crgarcia12/electronics-homeassistant-lightscontroll/PCB/schematics-v21-esp32s3-pcbway/readme-media/board-pcb2.png

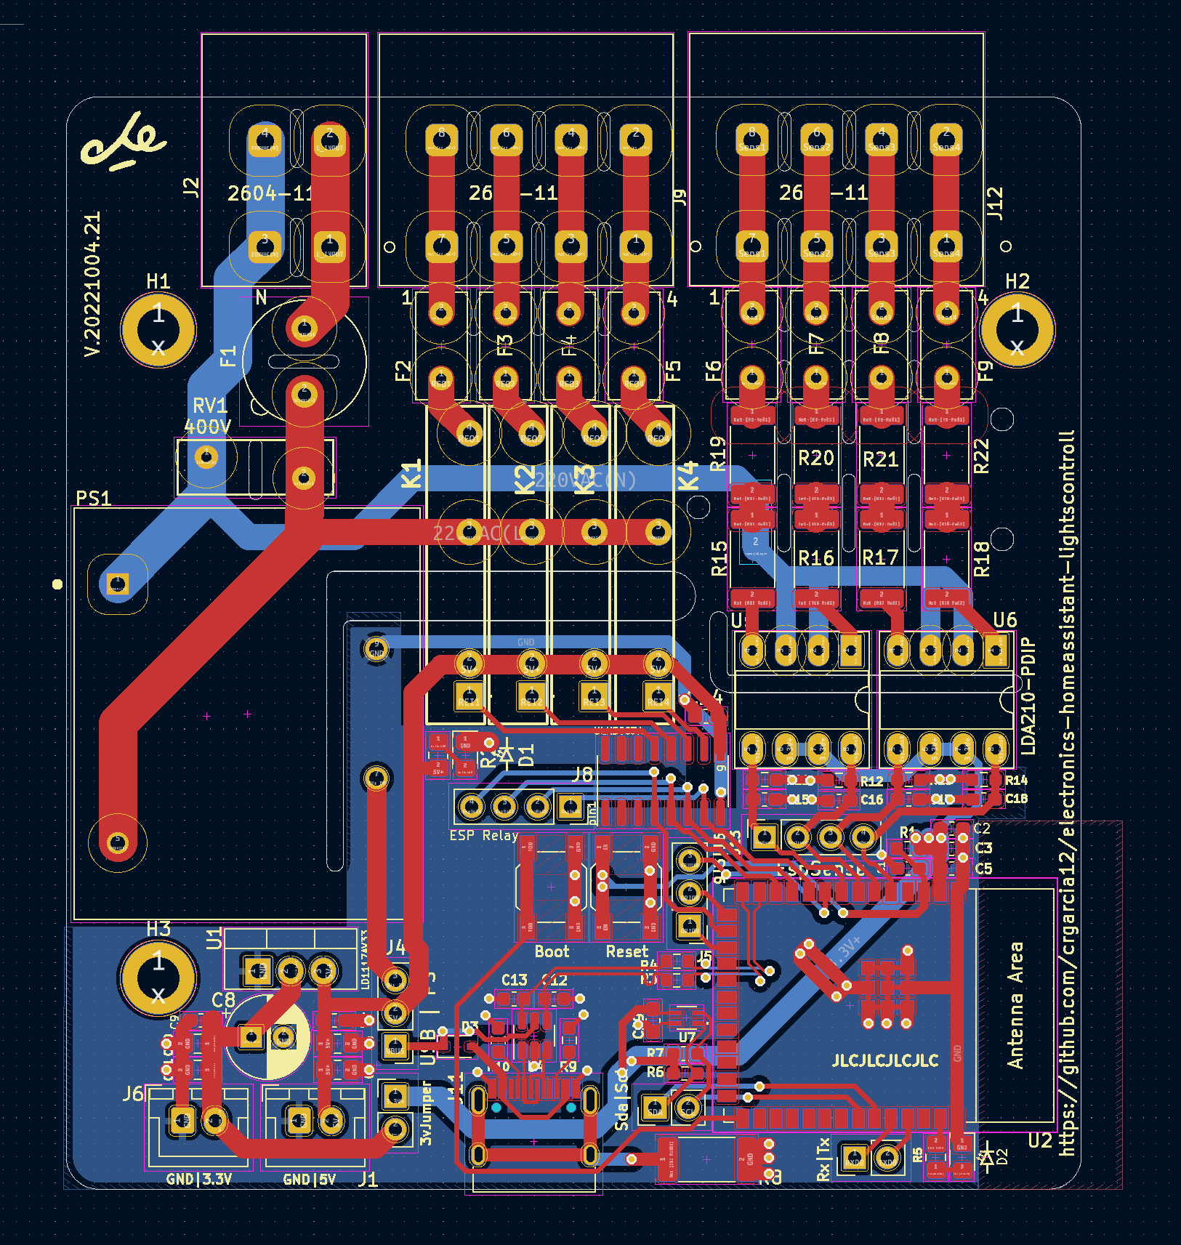
PCB/schematics-v21-esp32s3-pcbway/readme-media/board-pcb2.png
