crgarcia12/electronics-homeassistant-lightscontroll/PCB/schematics-v28.2-jlcpcb/readme-media/board-pcb-3d.jpg

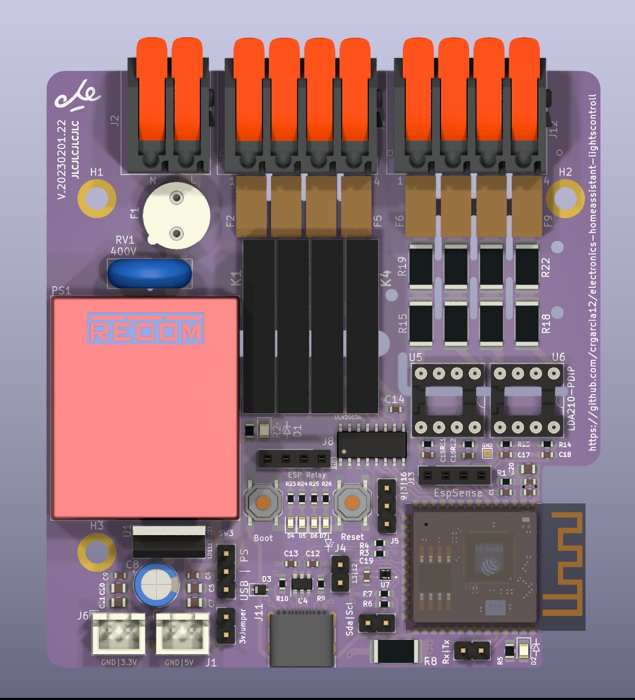
PCB/schematics-v28.2-jlcpcb/readme-media/board-pcb-3d.jpg
