crgarcia12/electronics-homeassistant-lightscontroll/readme-media/main-sensing-analysis/ILD755-22uF-off.jpeg

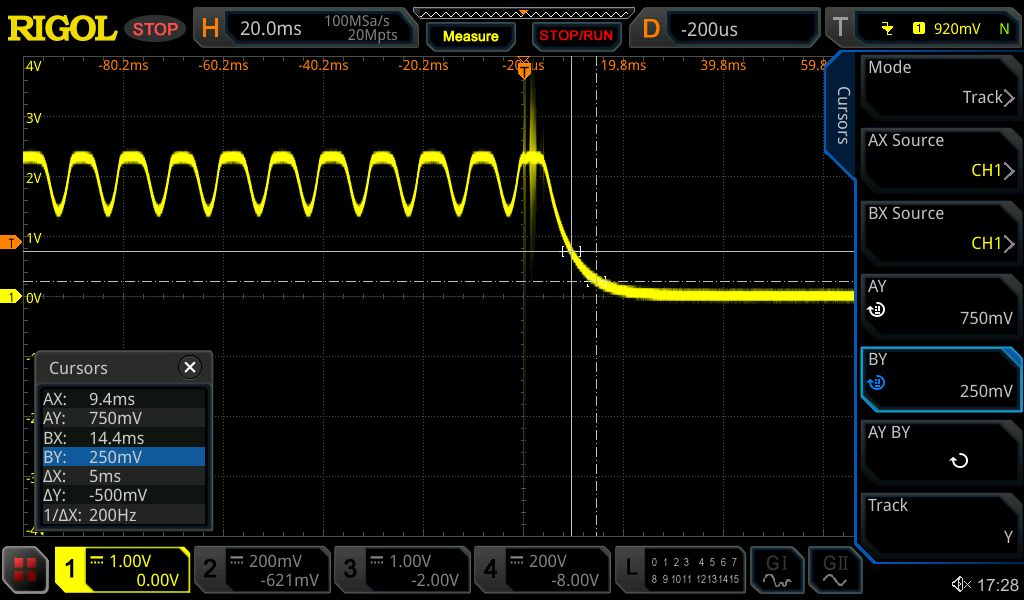
readme-media/main-sensing-analysis/ILD755-22uF-off.jpeg
