crgarcia12/electronics-homeassistant-lightscontroll/readme-media/main-sensing-analysis/ILD755-100uF-off.jpeg

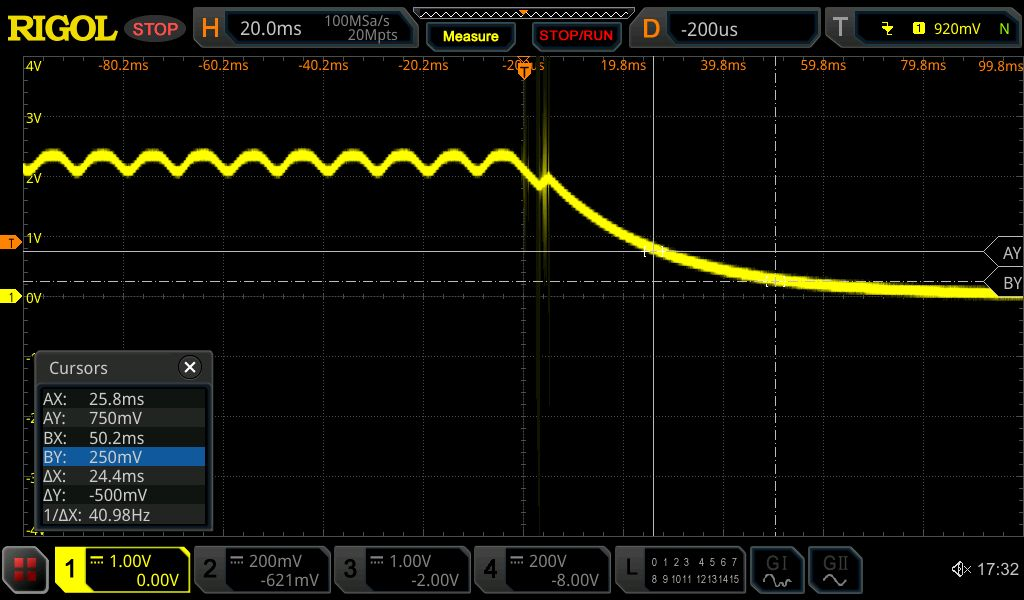
readme-media/main-sensing-analysis/ILD755-100uF-off.jpeg
