crgarcia12/electronics-homeassistant-lightscontroll/readme-media/main-sensing-analysis/LDA210-10uF-off.jpeg

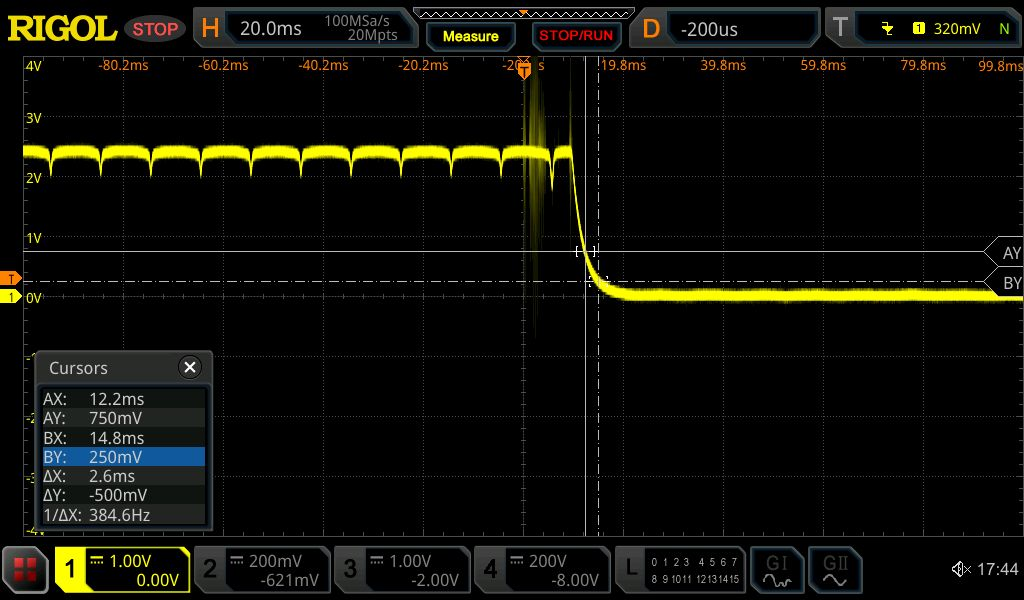
readme-media/main-sensing-analysis/LDA210-10uF-off.jpeg
