crgarcia12/electronics-homeassistant-lightscontroll/readme-media/scope/LDA210-ILD755-1.2023.09.03.off.png

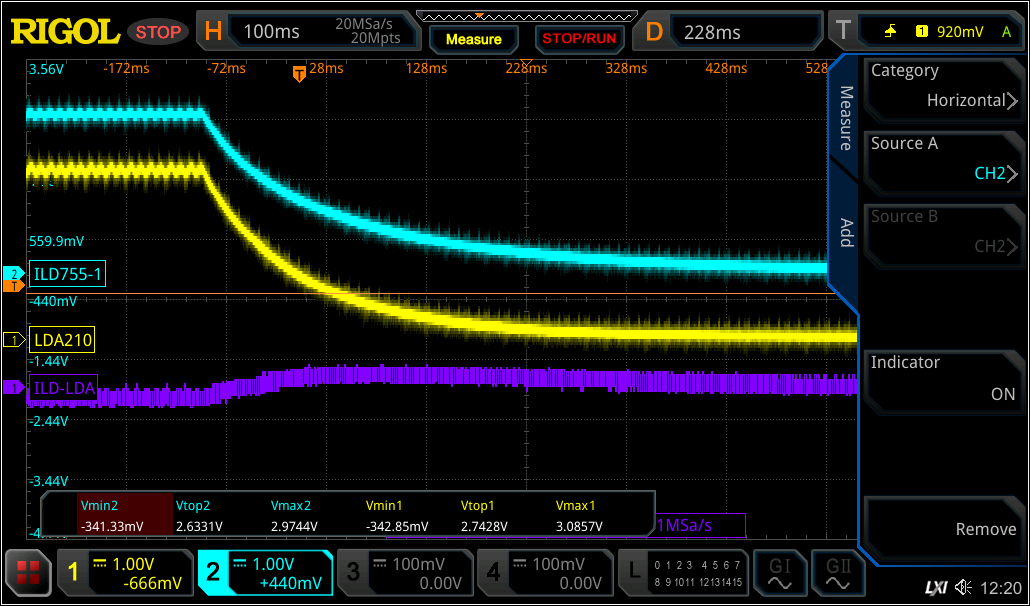
readme-media/scope/LDA210-ILD755-1.2023.09.03.off.png
