crgarcia12/electronics-homeassistant-lightscontroll/simulations/2024-08-19_11h31_58.png

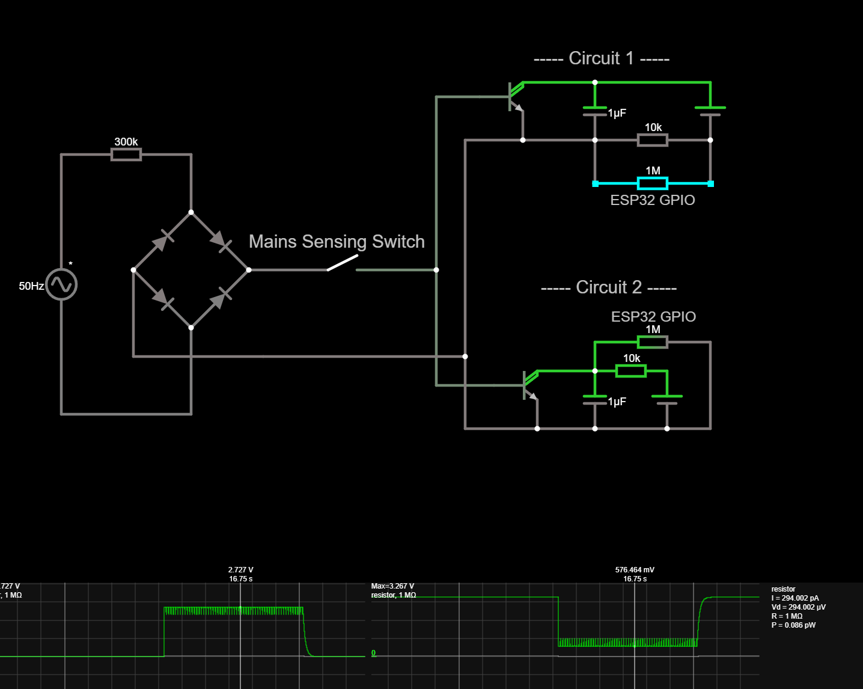
simulations/2024-08-19_11h31_58.png
