crgarcia12/electronics-homeassistant-lightscontroll/simulations/2024-08-19_11h50_34.png

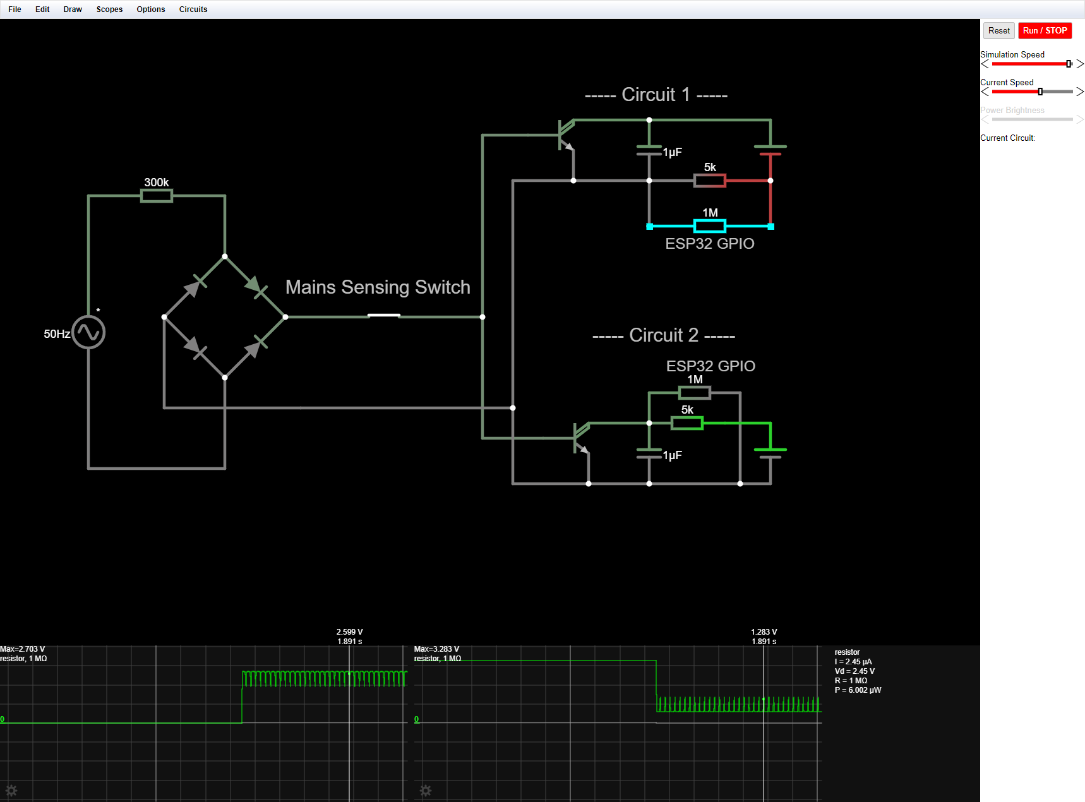
simulations/2024-08-19_11h50_34.png
