crgarcia12/electronics-homeassistant-lightscontroll/PCB/schematics-v16-espinside-jlcpcb/kicad/components-footprints/rac05-05sk/RAC05-05SK_277.step

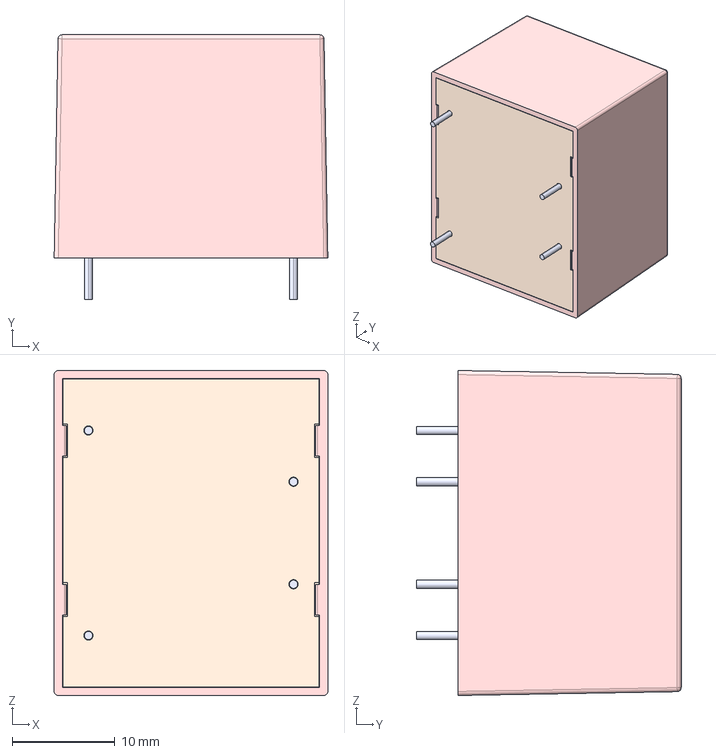
[picture p103: CAD file, 2021-09-07]
PCB/schematics-v16-espinside-jlcpcb/kicad/components-footprints/rac05-05sk/RAC05-05SK_277.step
26.7 x 25.8 x 31.7 mm
