crgarcia12/electronics-homeassistant-lightscontroll/PCB/schematics-v17-safety-jlcpcb/kicad/components-footprints/sht40/3d/SHT40-AD1B-R3--3DModel-STEP-231308.STEP

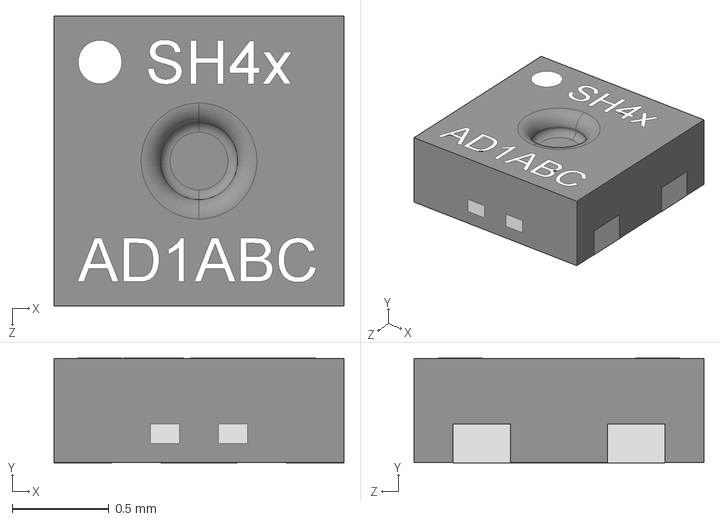
[picture p104: CAD file, 2022-02-28]
PCB/schematics-v17-safety-jlcpcb/kicad/components-footprints/sht40/3d/SHT40-AD1B-R3--3DModel-STEP-231308.STEP
1.50 x 0.542 x 1.50 mm
