crgarcia12/electronics-homeassistant-lightscontroll/PCB/schematics-v20-pcbway/kicad/components-footprints/pcn-105D3/eec.models/TE_Connectivity_-_PCN-124D3MHZ,000.step

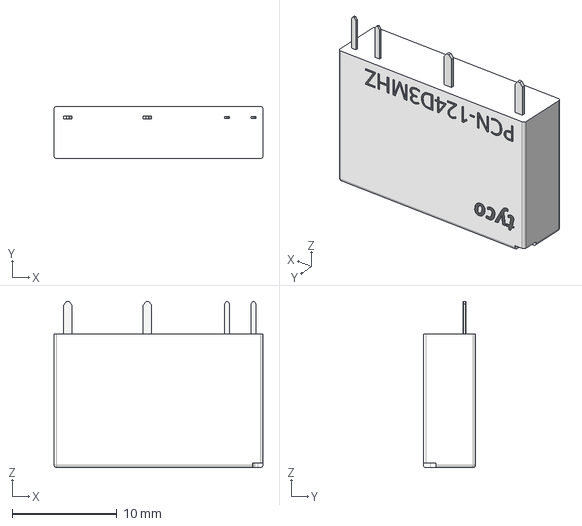
[picture p105: CAD file, 2021-11-05]
PCB/schematics-v20-pcbway/kicad/components-footprints/pcn-105D3/eec.models/TE_Connectivity_-_PCN-124D3MHZ,000.step
20.0 x 5.00 x 15.9 mm
