crgarcia12/electronics-homeassistant-lightscontroll/PCB/schematics-v24-1-jlcpcb/kicad/components-footprints/wago/wago-2604-1102/3D/CadenasModel/2604-1102.stp

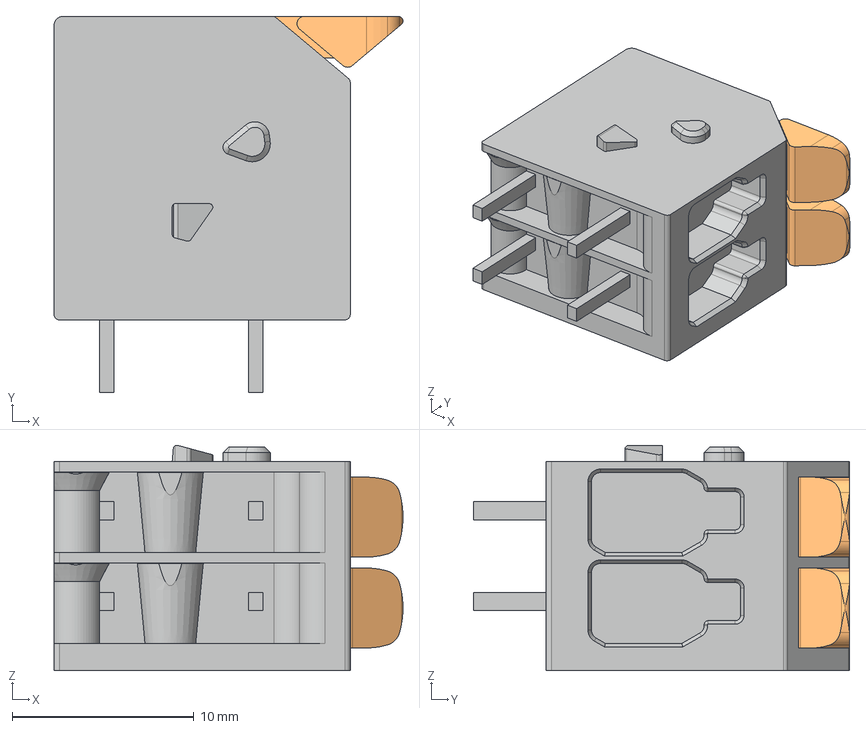
[picture p106: CAD file, 2022-06-03]
PCB/schematics-v24-1-jlcpcb/kicad/components-footprints/wago/wago-2604-1102/3D/CadenasModel/2604-1102.stp
19.2 x 20.7 x 12.4 mm
