crgarcia12/electronics-homeassistant-lightscontroll/PCB/schematics-v24-1-jlcpcb/kicad/components-footprints/wago/wago-2604-1104/3D/CadenasModel/2604-1104.stp

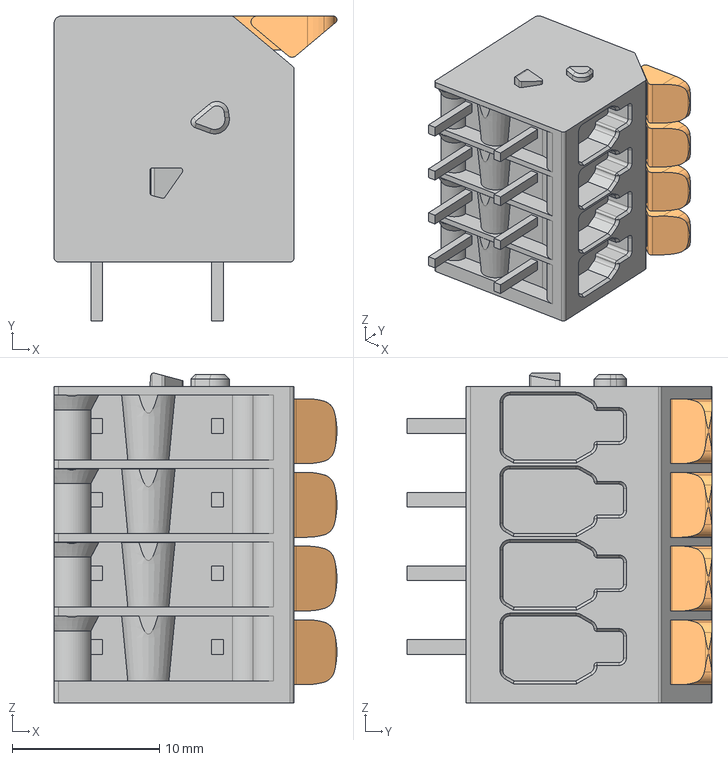
[picture p107: CAD file, 2022-06-03]
PCB/schematics-v24-1-jlcpcb/kicad/components-footprints/wago/wago-2604-1104/3D/CadenasModel/2604-1104.stp
19.2 x 20.7 x 22.4 mm
