crgarcia12/electronics-homeassistant-lightscontroll/PCB/schematics-v28.2-jlcpcb/kicad/components-footprints/RST-80-AMMO/RSTA_BEL.step

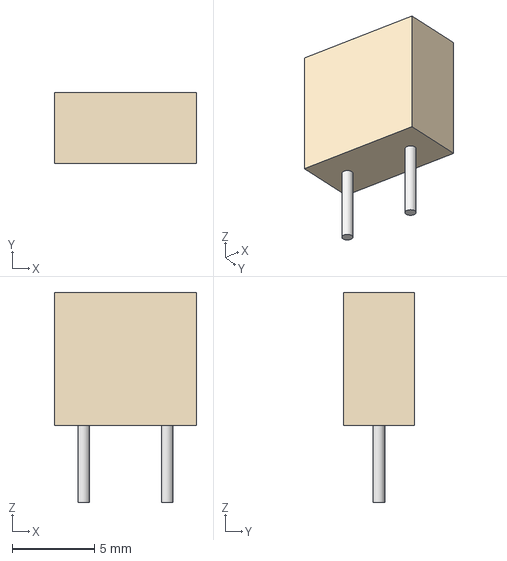
[picture p108: CAD file, 2022-06-03]
PCB/schematics-v28.2-jlcpcb/kicad/components-footprints/RST-80-AMMO/RSTA_BEL.step
8.66 x 4.29 x 12.8 mm
