crgarcia12/electronics-homeassistant-lightscontroll/PCB/schematics-v28.2-jlcpcb/kicad/components-footprints/usb-c/3D/HRO-20-Type-C-31-M-12.step

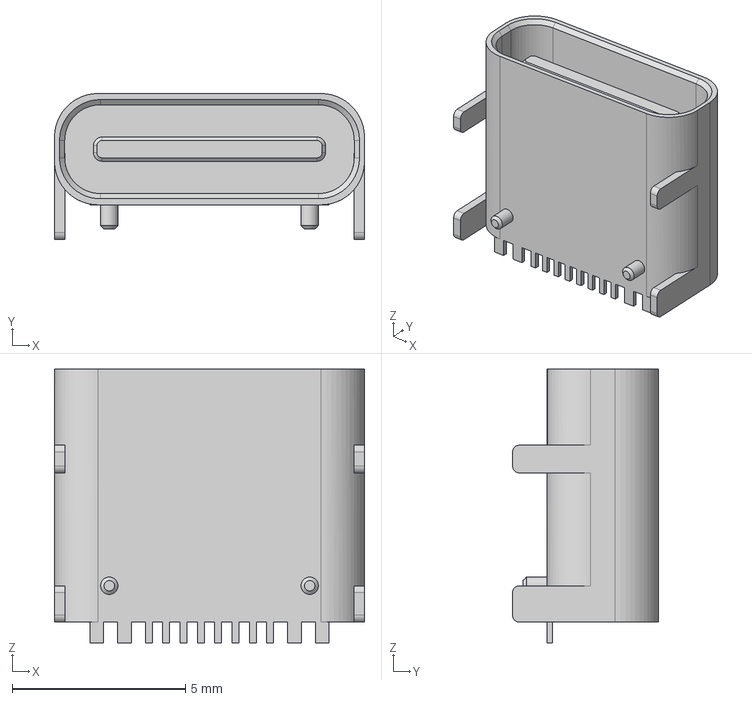
[picture p109: CAD file, 2022-03-14]
PCB/schematics-v28.2-jlcpcb/kicad/components-footprints/usb-c/3D/HRO-20-Type-C-31-M-12.step
8.94 x 4.21 x 7.90 mm
