crgarcia12/electronics-homeassistant-lightscontroll/readme-media/scope/LDA210-ILD755-1.2023.09.03.setup.jpg

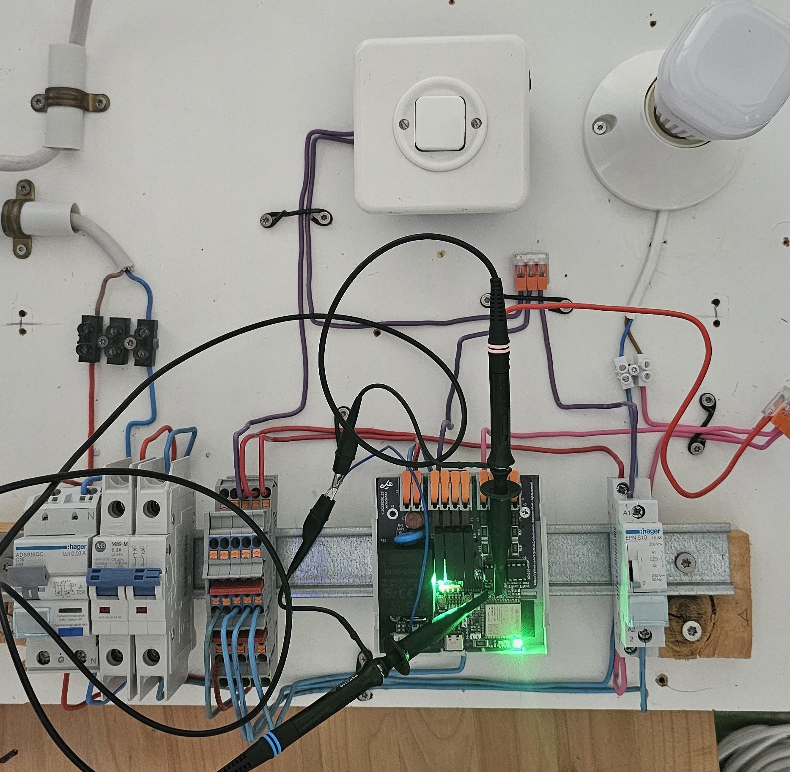
readme-media/scope/LDA210-ILD755-1.2023.09.03.setup.jpg
