crgarcia12/electronics-homeassistant-lightscontroll/current-issue/2022.08.02.13.34.25.391.failed.zoom.jpeg

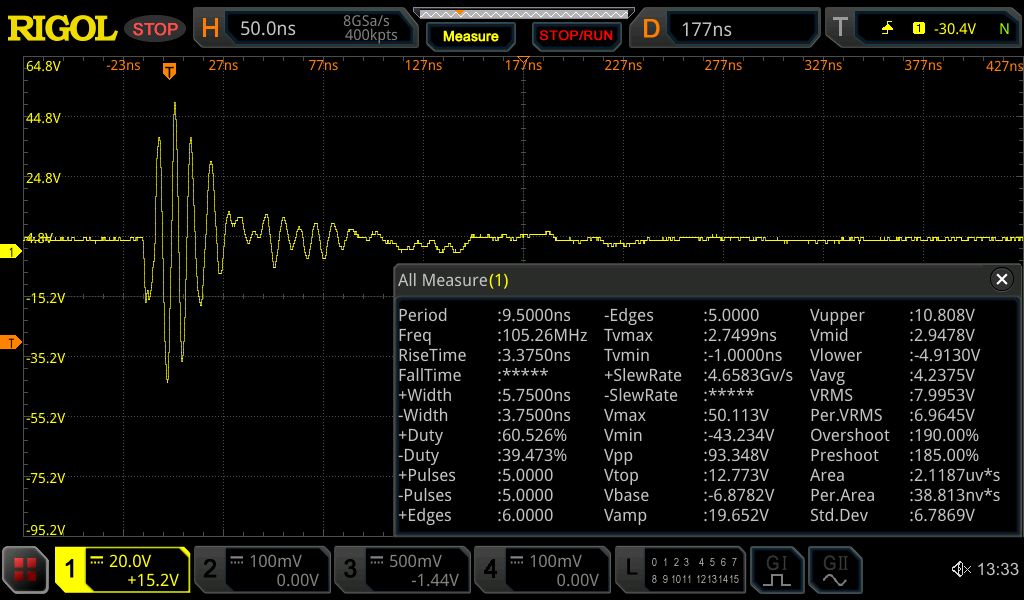
current-issue/2022.08.02.13.34.25.391.failed.zoom.jpeg
