crgarcia12/electronics-homeassistant-lightscontroll/current-issue/probes.JPG

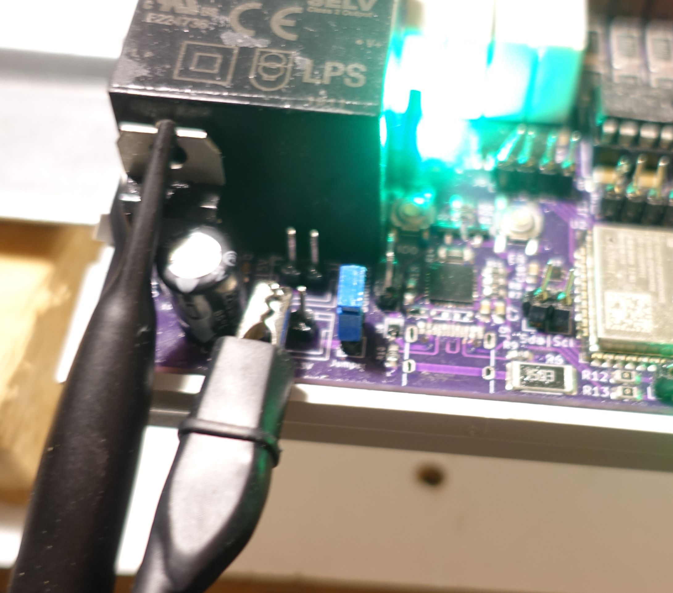
current-issue/probes.JPG
